MadScienceZone/readerboard/hardware/busylight/lighttree-smd.pdf

## lighttree-smd.pcb

## 1. Table of Contents (This Page) Created on Mon Sep 30 00:39:18 2024 2. top 3. bottom 4. outline 5. plated-drill 6. componentmask 7. soldermask 8. topsilk 9. bottomsilk 10. toppaste 11. bottompaste 12. topassembly 13. bottomassembly 14. fab

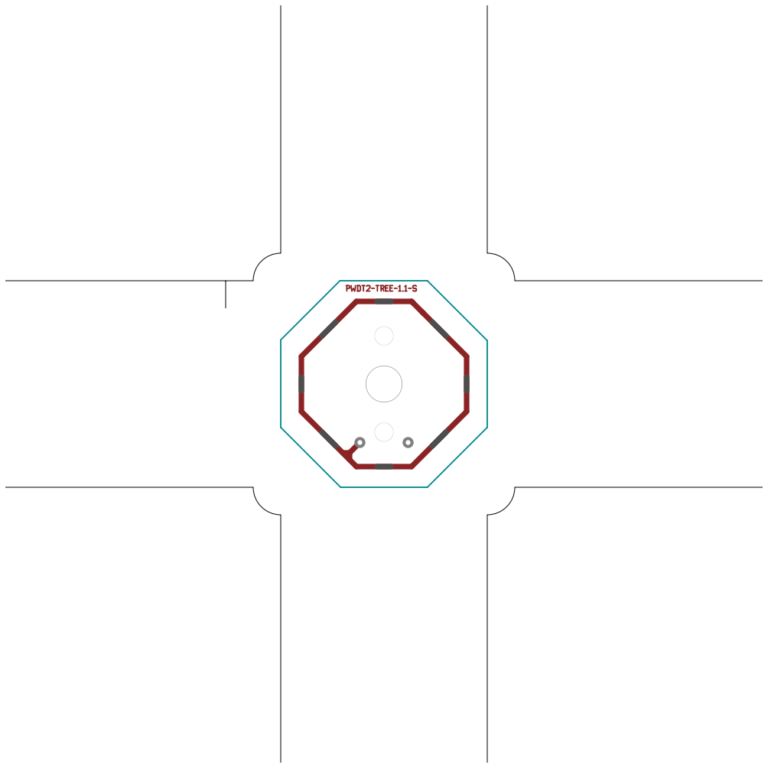
[picture p21: figure]

top, scale = 1:1.000

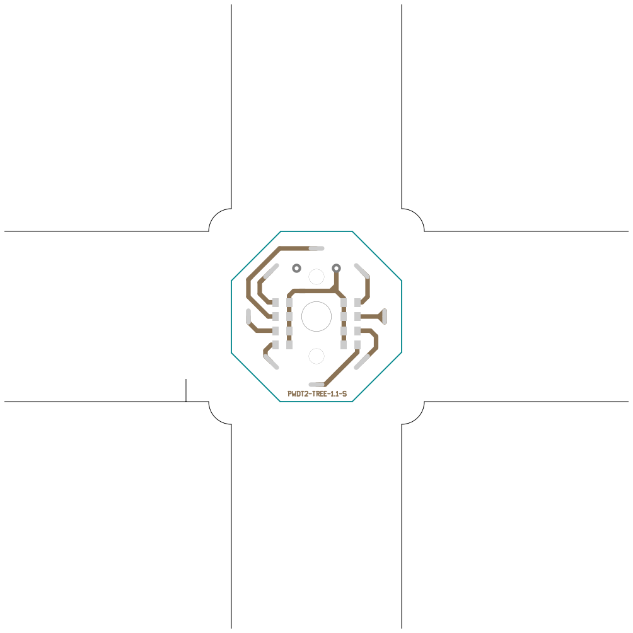
[picture p22: figure]

bottom (mirrored), scale = 1:1.000

outline, scale = 1:1.000 plated-drill, scale = 1:1.000

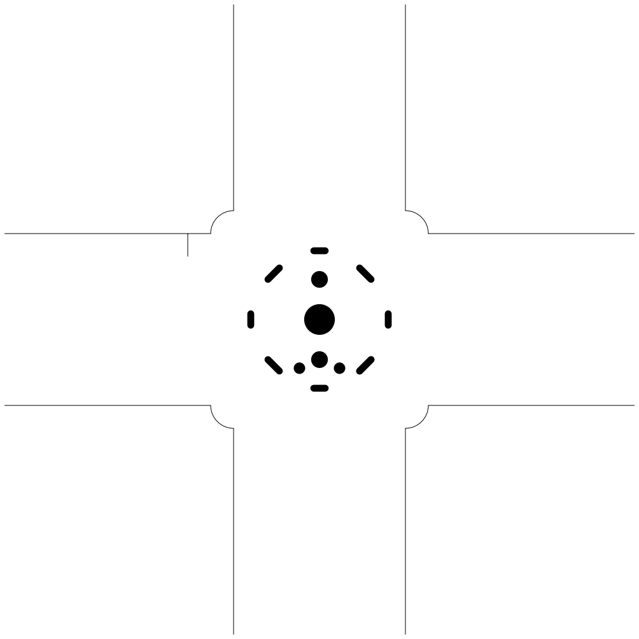
[picture p23: figure]

topmask, scale = 1:1.000

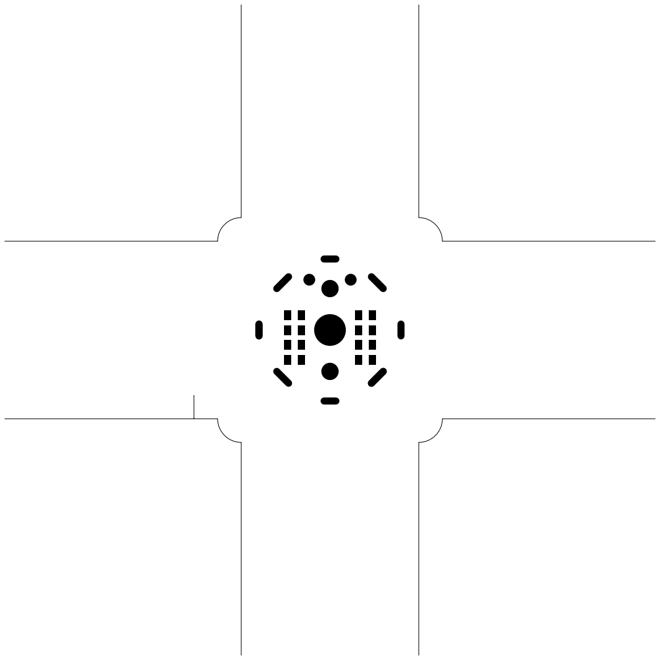
[picture p24: figure]

bottommask (mirrored), scale = 1:1.000

topsilk, scale = 1:1.000 bottomsilk (mirrored), scale = 1:1.000

toppaste, scale = 1:1.000 bottompaste (mirrored), scale = 1:1.000

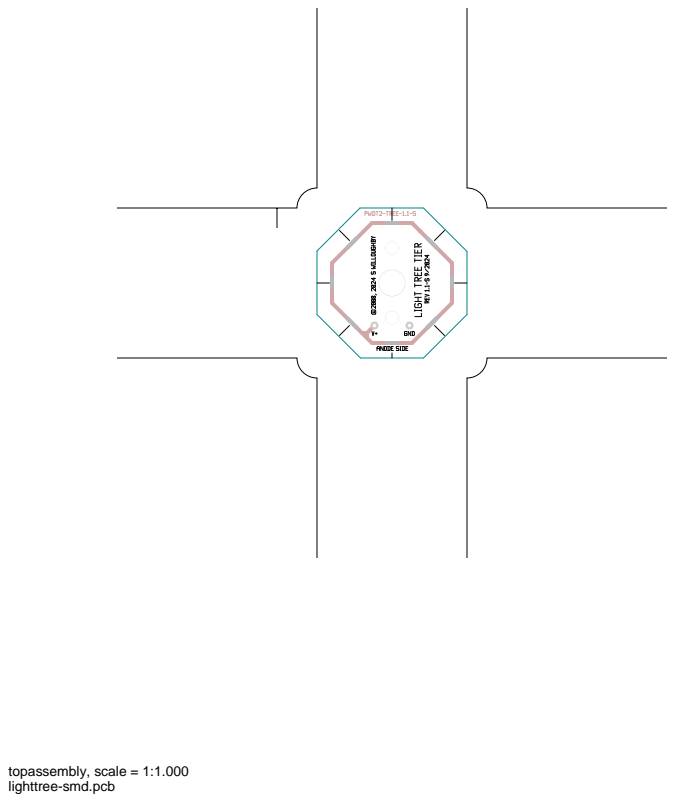
[picture p25: page 12]
topassembly, scale = 1:1.000

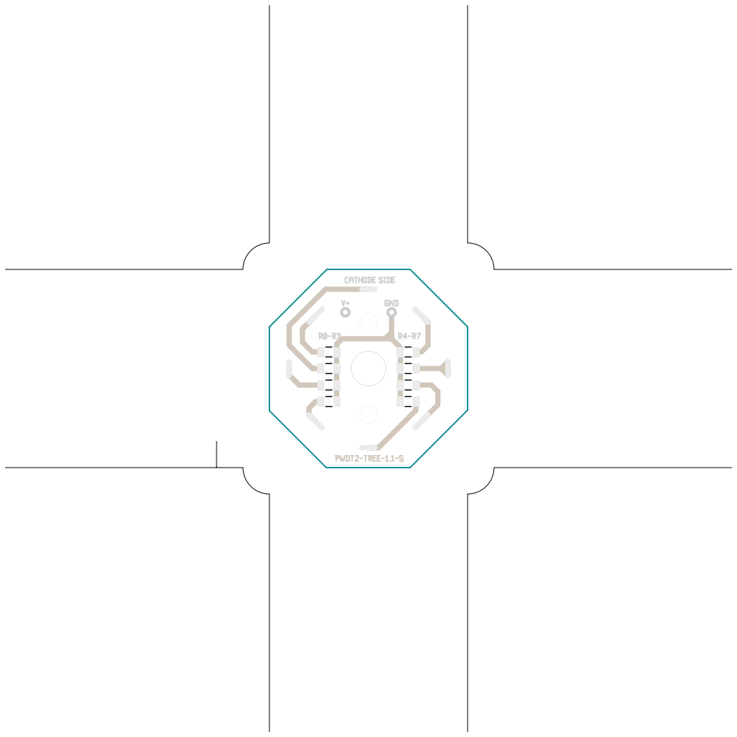
[picture p26: figure]

bottomassembly (mirrored), scale = 1:1.000

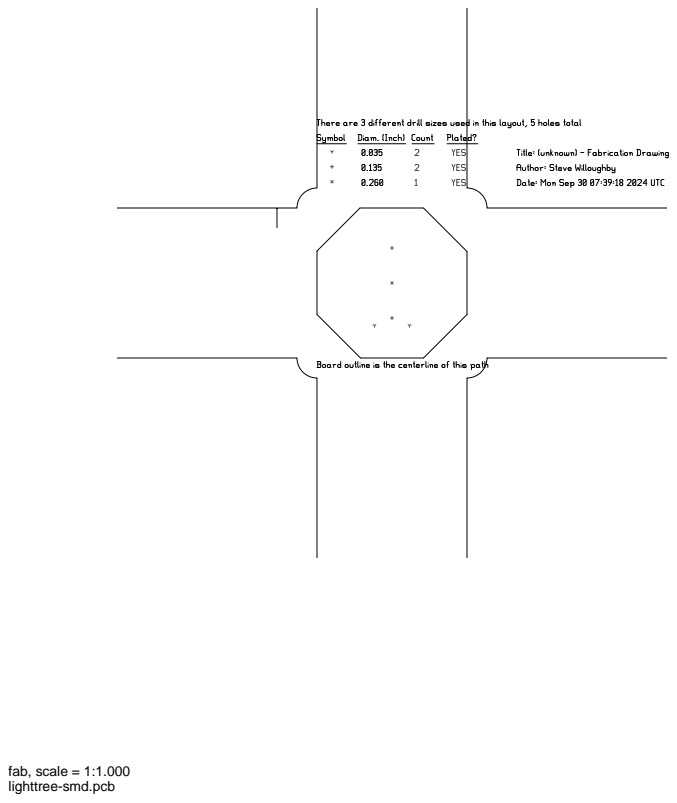
[picture p27: page 14]
fab, scale = 1:1.000
