MadScienceZone/readerboard/hardware/busylight/lighttree.pdf

## lighttree.pcb

## 1. Table of Contents (This Page) Created on Mon Sep 30 00:38:34 2024 2. top 3. bottom 4. outline 5. plated-drill 6. componentmask 7. soldermask 8. topsilk 9. bottomsilk 10. toppaste 11. bottompaste 12. topassembly 13. bottomassembly 14. fab

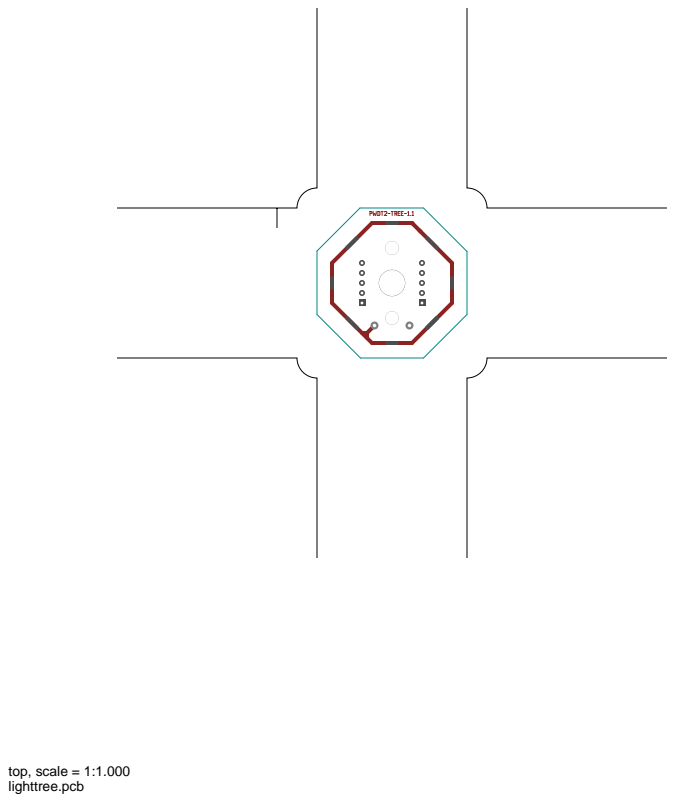
[picture p28: page 2]
top, scale = 1:1.000

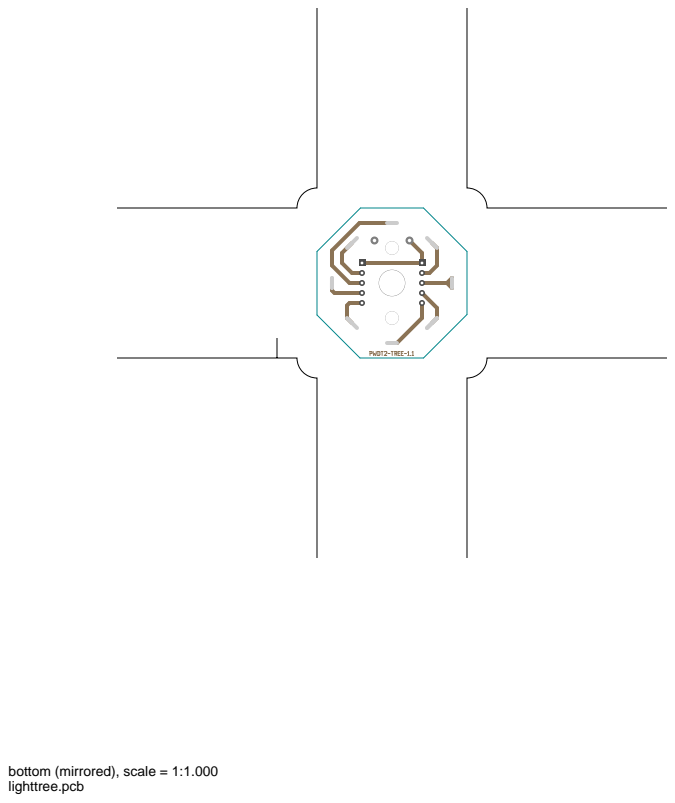
[picture p29: page 3]

bottom (mirrored), scale = 1:1.000

outline, scale = 1:1.000 plated-drill, scale = 1:1.000

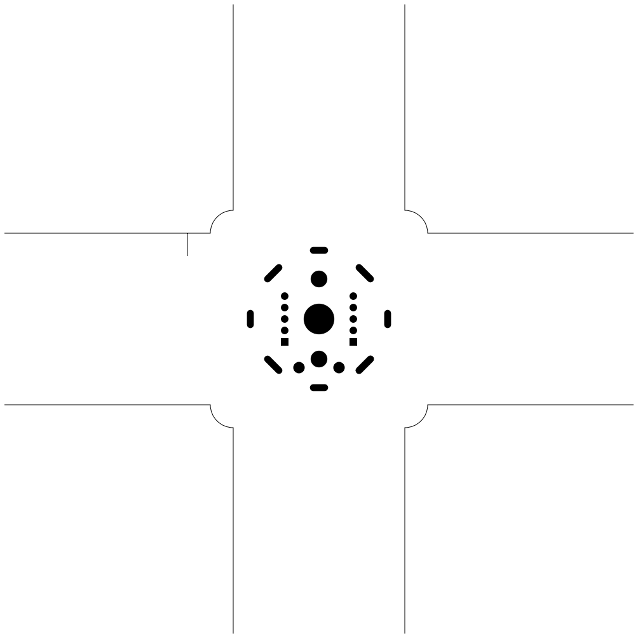
[picture p30: figure]

topmask, scale = 1:1.000

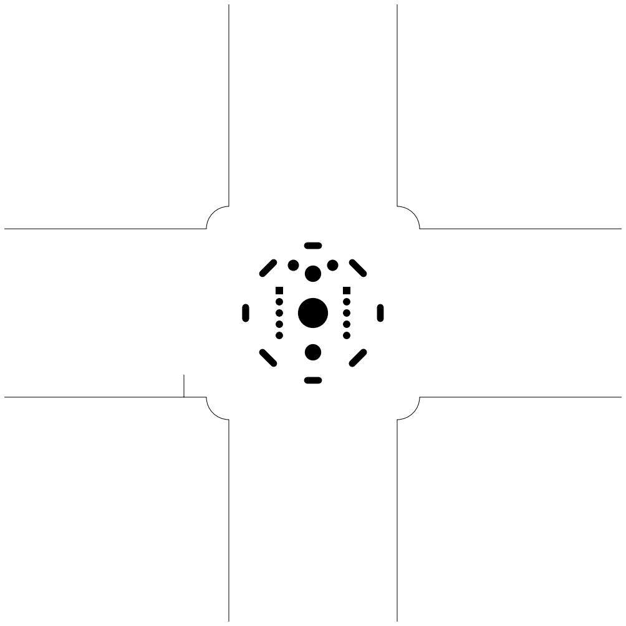
[picture p31: figure]

bottommask (mirrored), scale = 1:1.000

topsilk, scale = 1:1.000 bottomsilk (mirrored), scale = 1:1.000

toppaste, scale = 1:1.000 bottompaste (mirrored), scale = 1:1.000

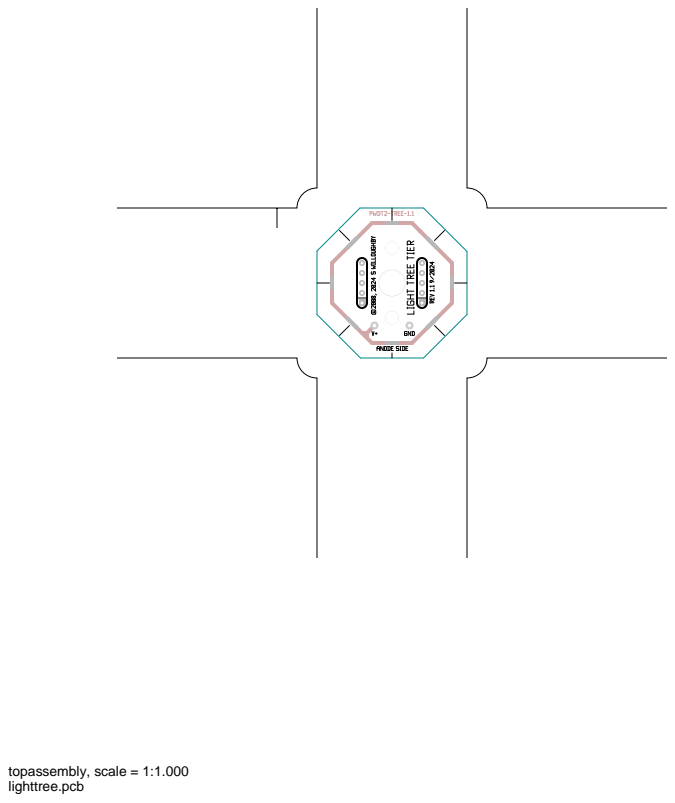
[picture p32: page 12]
topassembly, scale = 1:1.000

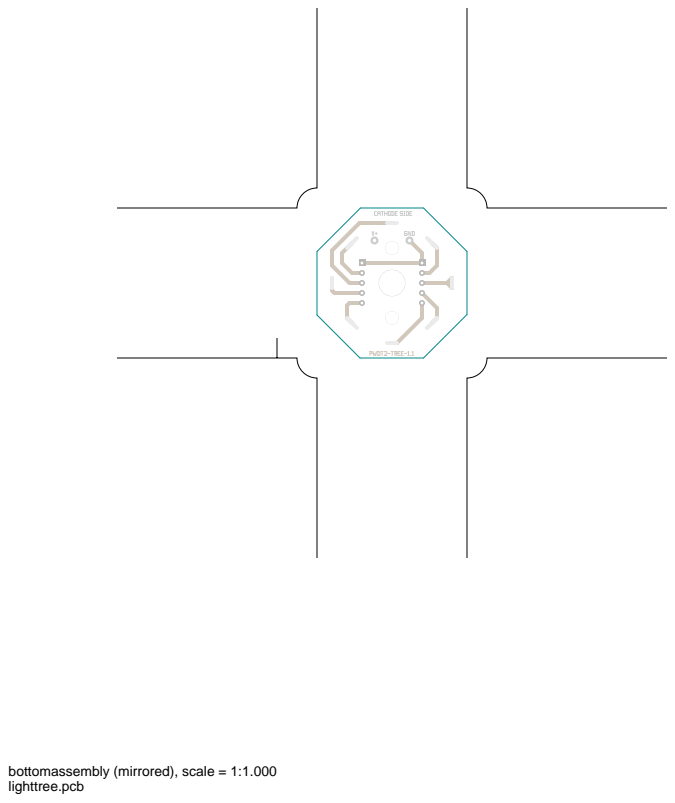
[picture p33: page 13]

bottomassembly (mirrored), scale = 1:1.000

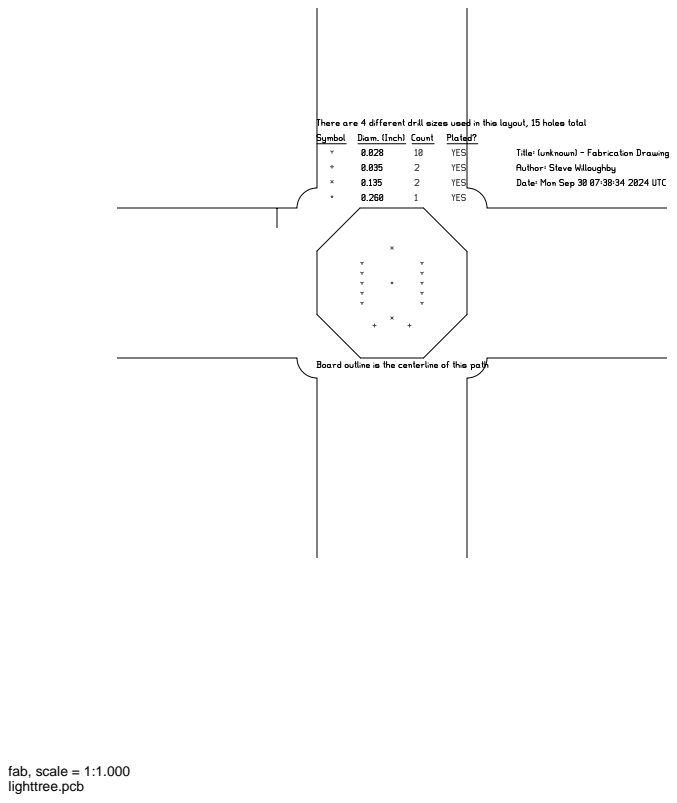
[picture p34: page 14]
fab, scale = 1:1.000
