MadScienceZone/readerboard/man/man1/setsn.pdf

SETSN(1) | General Commands Manual | SETSN(1)

NAME
setsn − Field program a newserial number into a device SYNOPSIS
setsn [−model type] −port name −sn serialno −speed rate
DESCRIPTION
After flashing a newfirmware image onto a newReaderboard or Busylight device, use this program to configure a unique serial number into its EEPROM.
OPTIONS
−model type
Specifies the hardware type being programmed. The value of type may be rb (the default), mono, or busylight, or any ofthe values which are accepted by rbserver(1)’sconfiguration file in the DeviceType field of the Devices list. While not strictly required, specifying this parameter may make it easier for setsn to correctly verify that the serial number has successfully been set.

−port name
Specifies the serial port’sdevice name on the system through which the device may be reached.

−sn serialno
The serial number to be set on the device. This must be no more than six characters, and should be plain ASCII characters, preferably alphanumerics. Serial numbers B00000−B00299 and RB0000−RB0299 are reserved for use by the original author.

−speed rate
Sets the baud rate at which to communicate with the target device.
AUTHOR
Steve Willoughby / steve@madscience.zone.
COPYRIGHT
Copyright © 2024 by Steven L. Willoughby,Aloha, Oregon, USA. All Rights Reserved. Distributed under the BSD 3-Clause License.
29-Sep-2024 | Readerboard/Busylight Project | 1
