MadScienceZone/readerboard/legacy/README.md

This directory contains the legacy Busylight support programs which have not yet been
converted to the combined busylight+readerboard model, where they will work hand-in-hand
with `rbserver` to update a set of devices.
