MadScienceZone/readerboard/doc/images/busylight_tree-assembly-0.png

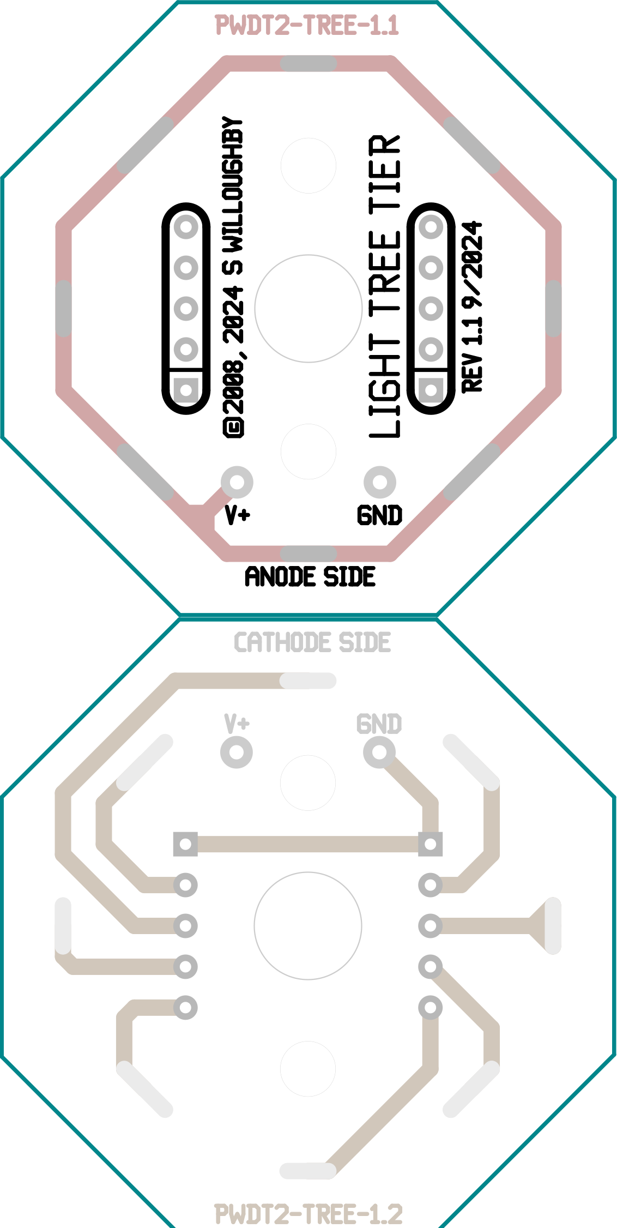
doc/images/busylight_tree-assembly-0.png
