MadScienceZone/readerboard/hardware/ada/adashield.kicad_sch

## KiCad design hardware/ada/adashield.kicad_sch (2024-10-30)

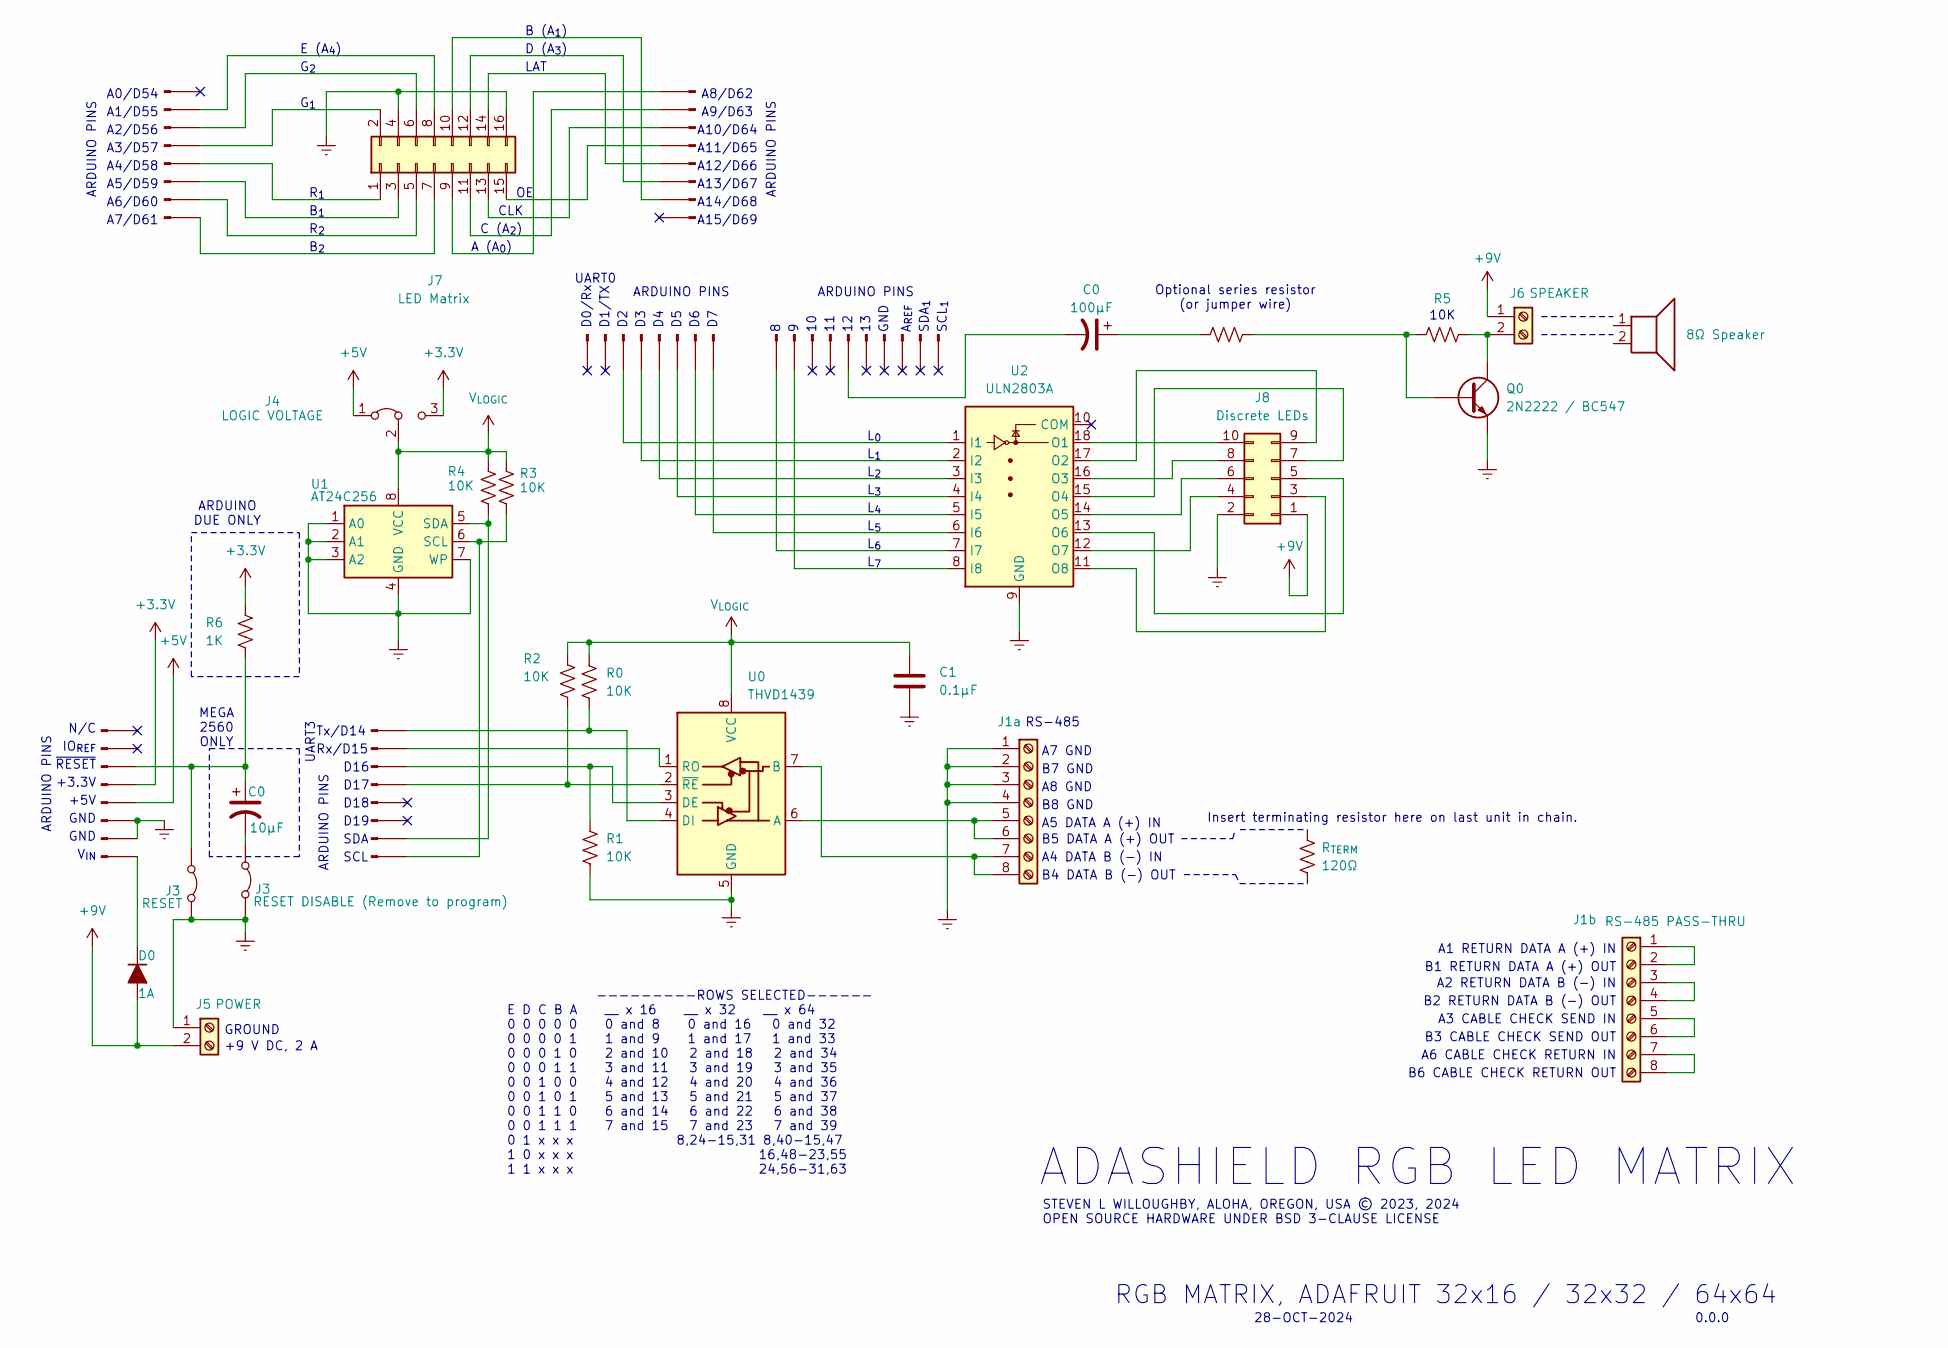
[picture p107: schematic adashield.kicad_sch]

Parts:
C0: 100μF
C1: 0.1µF
D0: 1A
J1a: Screw_Terminal_01x08
J1b: RS-485 PASS-THRU
J3, J4: Conn_01x08_Pin
J5: POWER
J6: SPEAKER
J7: LED Matrix
J8: Discrete LEDs
LS1: 8Ω Speaker
Q0: 2N2222 / BC547
R0, R1, R2, R3, R4: 10K
R5, R55: R_US
R6: 1K
R_{TERM}: 120Ω
U0: THVD1439; SOIC-8_3.9x4.9mm_P1.27mm
U1: AT24C256; SOIC-8_3.9x4.9mm_P1.27mm
U2: ULN2803A

Connections:
+3.3V: J3.4, J4.3 (B), R6.1
+5V: J3.5, J4.1 (A)
+9V: D0.2 (A), J5.2, J6.1, J8.1
Earth: J7.4, J7.16
GNDREF: C1.2, J1a.1, J1a.2, J1a.3, J1a.4, J3.2 (B), J3.6, J3.7, J5.1, J8.2, Q0.3 (E), R1.2, U0.5 (GND), U1.1 (A0), U1.2 (A1), U1.3 (A2), U1.4 (GND), U1.7 (WP), U2.9 (GND)
unnamed: C0.1, J3.1 (A), J3.3, R6.2, R55.1
unnamed: C0.2, J3.1 (A)
unnamed: D0.1 (K), J3.8
unnamed: J1a.5, J1a.6, U0.6 (A)
unnamed: J1a.7, J1a.8, U0.7 (B)
unnamed: J1b.1, J1b.2
unnamed: J1b.3, J1b.4
unnamed: J1b.5, J1b.6
unnamed: J1b.7, J1b.8
unnamed: J4.1 (A), R0.2, U0.4 (DI)
unnamed: J4.2 (C), U0.1 (RO)
unnamed: J4.3 (B), R1.1, U0.3 (DE)
unnamed: J4.4, R2.2, U0.2 (~RE)
unnamed: J4.7, R4.2, U1.5 (SDA)
unnamed: J4.8, R3.2, U1.6 (SCL)
unnamed: J6.2, Q0.1 (C), R5.2
unnamed: J8.3, U2.11 (O8)
unnamed: J8.4, U2.12 (O7)
unnamed: J8.5, U2.13 (O6)
unnamed: J8.6, U2.14 (O5)
unnamed: J8.7, U2.15 (O4)
unnamed: J8.8, U2.16 (O3)
unnamed: J8.9, U2.17 (O2)
unnamed: J8.10, U2.18 (O1)
unnamed: Q0.2 (B), R5.1, R55.2
V_{LOGIC}: C1.1, J4.2 (C), R0.1, R2.1, R3.1, R4.1, U0.8 (VCC), U1.8 (VCC)

Notes on the sheet:
C (A_{2})
B4 DATA B (-) OUT
A0/D54
28-OCT-2024
+5V
ARDUINO PINS
ARDUINO DUE ONLY
A10/D64
A13/D67
B_{1}
CLK
GND
RS-485
UART0
SDA
A3/D57
RGB MATRIX, ADAFRUIT 32x16 / 32x32 / 64x64
A9/D63
G_{1}
A14/D68
SCL
0.0.0
A6 CABLE CHECK RETURN IN
R_{2}
A7/D61
---------ROWS SELECTED------ E D C B A __ x 16 __ x 32 __ x 64 0 0 0 0 0 0 and 8 0 and 16 0 and 32 0 0 0 0 1 1 and 9 1 and 17 1 and 33 0 0 0 1 0 2 and 10 2 and 18 2 and 34 0 0 0 1 1 3 and 11 3 and 19 3 and 35 0 0 1 0 0 4 and 12 4 and 20 4 and 36 0 0 1 0 1 5 and 13 5 and 21 5 and 37 0 0 1 1 0 6 and 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
B1 RETURN DATA A (+) OUT
L_{2}
A7 GND
B (A_{1})
D18
Optional series resistor (or jumper wire)
A3 CABLE CHECK SEND IN
A8/D62
A_{REF}
L_{5}
B8 GND
+9 V DC, 2 A
STEVEN L WILLOUGHBY, ALOHA, OREGON, USA © 2023, 2024 OPEN SOURCE HARDWARE UNDER BSD 3-CLAUSE LICENSE
MEGA 2560 ONLY
A11/D65
D1/TX
B5 DATA A (+) OUT
B_{2}
GROUND
Tx/D14
D0/Rx
A4 DATA B (-) IN
R_{1}
LAT
L_{6}
L_{3}
A1 RETURN DATA A (+) IN
L_{4}
SCL_{1}
B7 GND
10K
~{RESET}
E (A_{4})
B2 RETURN DATA B (-) OUT
N/C
D16
A5 DATA A (+) IN
Rx/D15
A (A_{0})
D19
A8 GND
A2 RETURN DATA B (-) IN
L_{0}
B6 CABLE CHECK RETURN OUT
A5/D59
+3.3V
A12/D66
IO_{REF}
L_{7}
B3 CABLE CHECK SEND OUT
D (A_{3})
L_{1}
A1/D55
ADASHIELD RGB LED MATRIX
A4/D58
G_{2}
A2/D56
D17
V_{IN}
SDA_{1}
UART3
Insert terminating resistor here on last unit in chain.
A15/D69
A6/D60
