MadScienceZone/readerboard/hardware/ada/adashield_qs.kicad_sch

## KiCad design hardware/ada/adashield_qs.kicad_sch (2024-10-29)

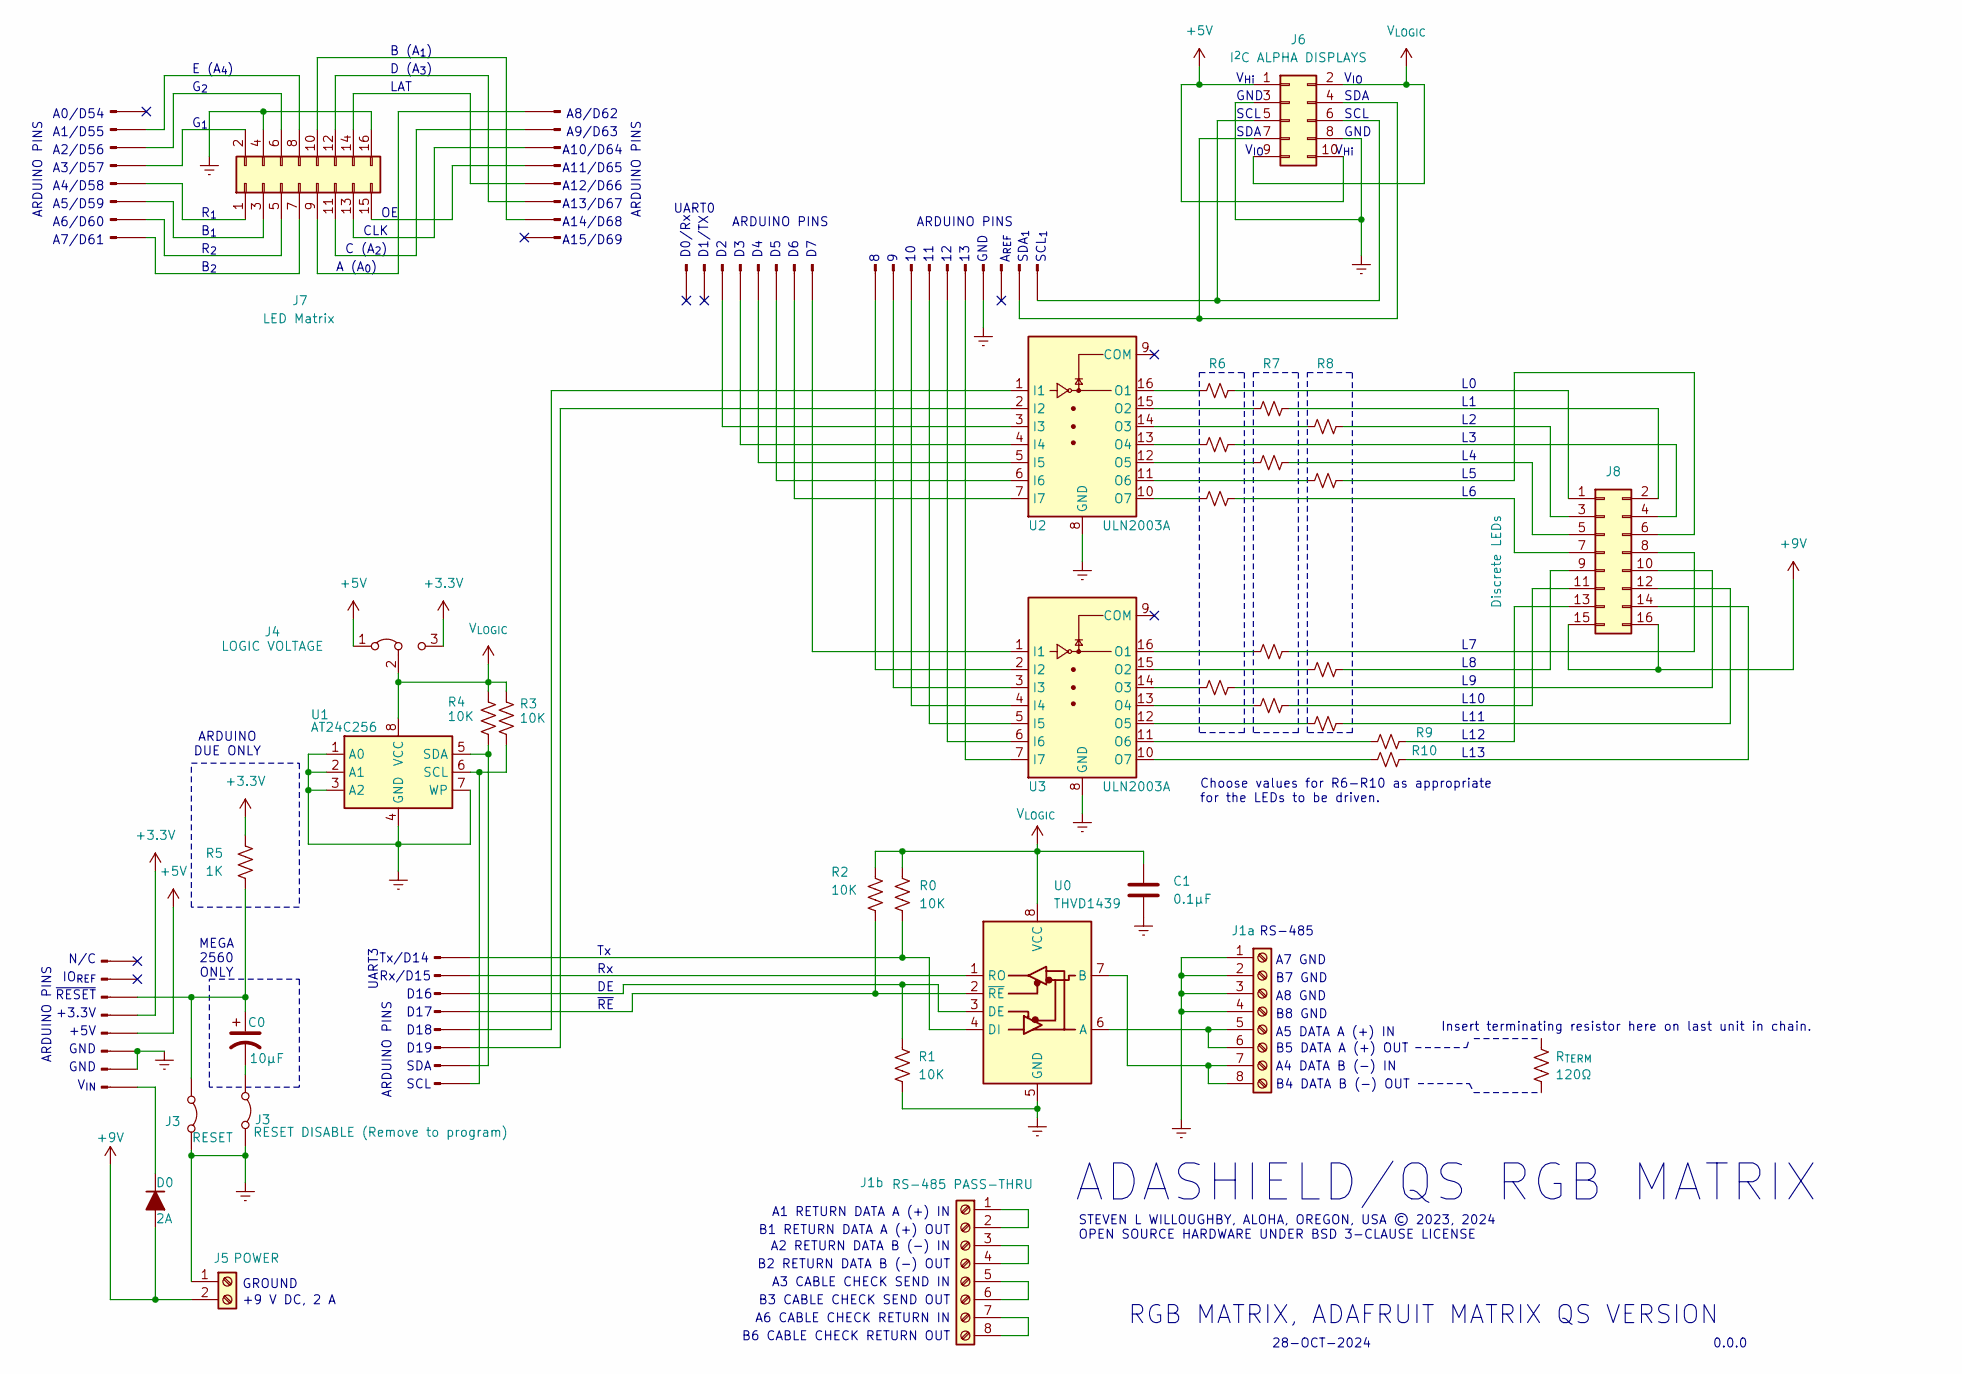
[picture p108: schematic adashield_qs.kicad_sch]

Parts:
C0: 10µF
C1: 0.1µF
D0: 2A
J1a: Screw_Terminal_01x08
J1b: RS-485 PASS-THRU
J3, J4: Conn_01x08_Pin
J5: POWER
J6: I^{2}C ALPHA DISPLAYS
J7: LED Matrix
J8: Discrete LEDs
R0, R1, R2, R3, R4: 10K
R5: 1K
R6, R7, R8, R9, R10, R11, R12, R13, R15, R16, R17: R_Small_US
R_{TERM}: 120Ω
U0: THVD1439; SOIC-8_3.9x4.9mm_P1.27mm
U1: AT24C256; SOIC-8_3.9x4.9mm_P1.27mm
U2, U3: ULN2003A

Connections:
+3.3V: J3.4, J4.3 (B), R5.1
+5V: J3.5, J4.1 (A), J6.1, J6.10
+9V: D0.2 (A), J5.2, J8.15, J8.16
Earth: J7.4, J7.16
GNDREF: C1.2, J1a.1, J1a.2, J1a.3, J1a.4, J3.2 (B), J3.6, J3.7, J5.1, J6.3, J6.8, R1.2, U0.5 (GND), U1.1 (A0), U1.2 (A1), U1.3 (A2), U1.4 (GND), U1.7 (WP), U2.8 (GND), U3.8 (GND)
unnamed: C0.1, J3.1 (A), J3.3, R5.2
unnamed: C0.2, J3.1 (A)
unnamed: D0.1 (K), J3.8
unnamed: J1a.5, J1a.6, U0.6 (A)
unnamed: J1a.7, J1a.8, U0.7 (B)
unnamed: J1b.1, J1b.2
unnamed: J1b.3, J1b.4
unnamed: J1b.5, J1b.6
unnamed: J1b.7, J1b.8
unnamed: J4.1 (A), R0.2, U0.4 (DI)
unnamed: J4.2 (C), U0.1 (RO)
unnamed: J4.3 (B), R1.1, U0.3 (DE)
unnamed: J4.4, R2.2, U0.2 (~RE)
unnamed: J4.5, U2.1 (I1)
unnamed: J4.6, U2.2 (I2)
unnamed: J4.7, R4.2, U1.5 (SDA)
unnamed: J4.8, R3.2, U1.6 (SCL)
unnamed: J6.4, J6.7
unnamed: J6.5, J6.6
unnamed: J8.1, R6.2
unnamed: J8.2, R7.2
unnamed: J8.3, R8.2
unnamed: J8.4, R7.2
unnamed: J8.5, R11.2
unnamed: J8.6, R15.2
unnamed: J8.7, R8.2
unnamed: J8.8, R12.2
unnamed: J8.9, R16.2
unnamed: J8.10, R9.2
unnamed: J8.11, R13.2
unnamed: J8.12, R17.2
unnamed: J8.13, R9.2
unnamed: J8.14, R10.2
unnamed: R6.1, U2.16 (O1)
unnamed: R7.1, U2.13 (O4), U2.15 (O2)
unnamed: R8.1, U2.10 (O7), U2.14 (O3)
unnamed: R9.1, U3.11 (O6), U3.14 (O3)
unnamed: R10.1, U3.10 (O7)
unnamed: R11.1, U2.12 (O5)
unnamed: R12.1, U3.16 (O1)
unnamed: R13.1, U3.13 (O4)
unnamed: R15.1, U2.11 (O6)
unnamed: R16.1, U3.15 (O2)
unnamed: R17.1, U3.12 (O5)
V_{LOGIC}: C1.1, J4.2 (C), J6.2, J6.9, R0.1, R2.1, R3.1, R4.1, U0.8 (VCC), U1.8 (VCC)

Notes on the sheet:
C (A_{2})
B4 DATA B (-) OUT
A0/D54
28-OCT-2024
L12
+5V
ARDUINO PINS
ARDUINO DUE ONLY
A10/D64
A13/D67
B_{1}
CLK
GND
L13
RS-485
UART0
SDA
L10
A3/D57
RGB MATRIX, ADAFRUIT MATRIX QS VERSION
A9/D63
G_{1}
~{RE}
A14/D68
SCL
0.0.0
A6 CABLE CHECK RETURN IN
V_{IO}
R_{2}
A7/D61
B1 RETURN DATA A (+) OUT
Choose values for R6-R10 as appropriate for the LEDs to be driven.
A7 GND
B (A_{1})
D18
A3 CABLE CHECK SEND IN
A8/D62
A_{REF}
B8 GND
+9 V DC, 2 A
STEVEN L WILLOUGHBY, ALOHA, OREGON, USA © 2023, 2024 OPEN SOURCE HARDWARE UNDER BSD 3-CLAUSE LICENSE
MEGA 2560 ONLY
A11/D65
D1/TX
B5 DATA A (+) OUT
B_{2}
GROUND
Tx/D14
D0/Rx
A4 DATA B (-) IN
R_{1}
V_{Hi}
LAT
A1 RETURN DATA A (+) IN
SCL_{1}
B7 GND
L11
~{RESET}
E (A_{4})
B2 RETURN DATA B (-) OUT
N/C
D16
A5 DATA A (+) IN
Rx/D15
A (A_{0})
D19
A8 GND
A2 RETURN DATA B (-) IN
B6 CABLE CHECK RETURN OUT
A5/D59
+3.3V
A12/D66
IO_{REF}
B3 CABLE CHECK SEND OUT
D (A_{3})
A1/D55
ADASHIELD/QS RGB MATRIX
A4/D58
G_{2}
A2/D56
D17
V_{IN}
SDA_{1}
UART3
Insert terminating resistor here on last unit in chain.
A15/D69
A6/D60
