MadScienceZone/readerboard/hardware/busylight/busylight.kicad_sch

## KiCad design hardware/busylight/busylight.kicad_sch (2024-10-28)

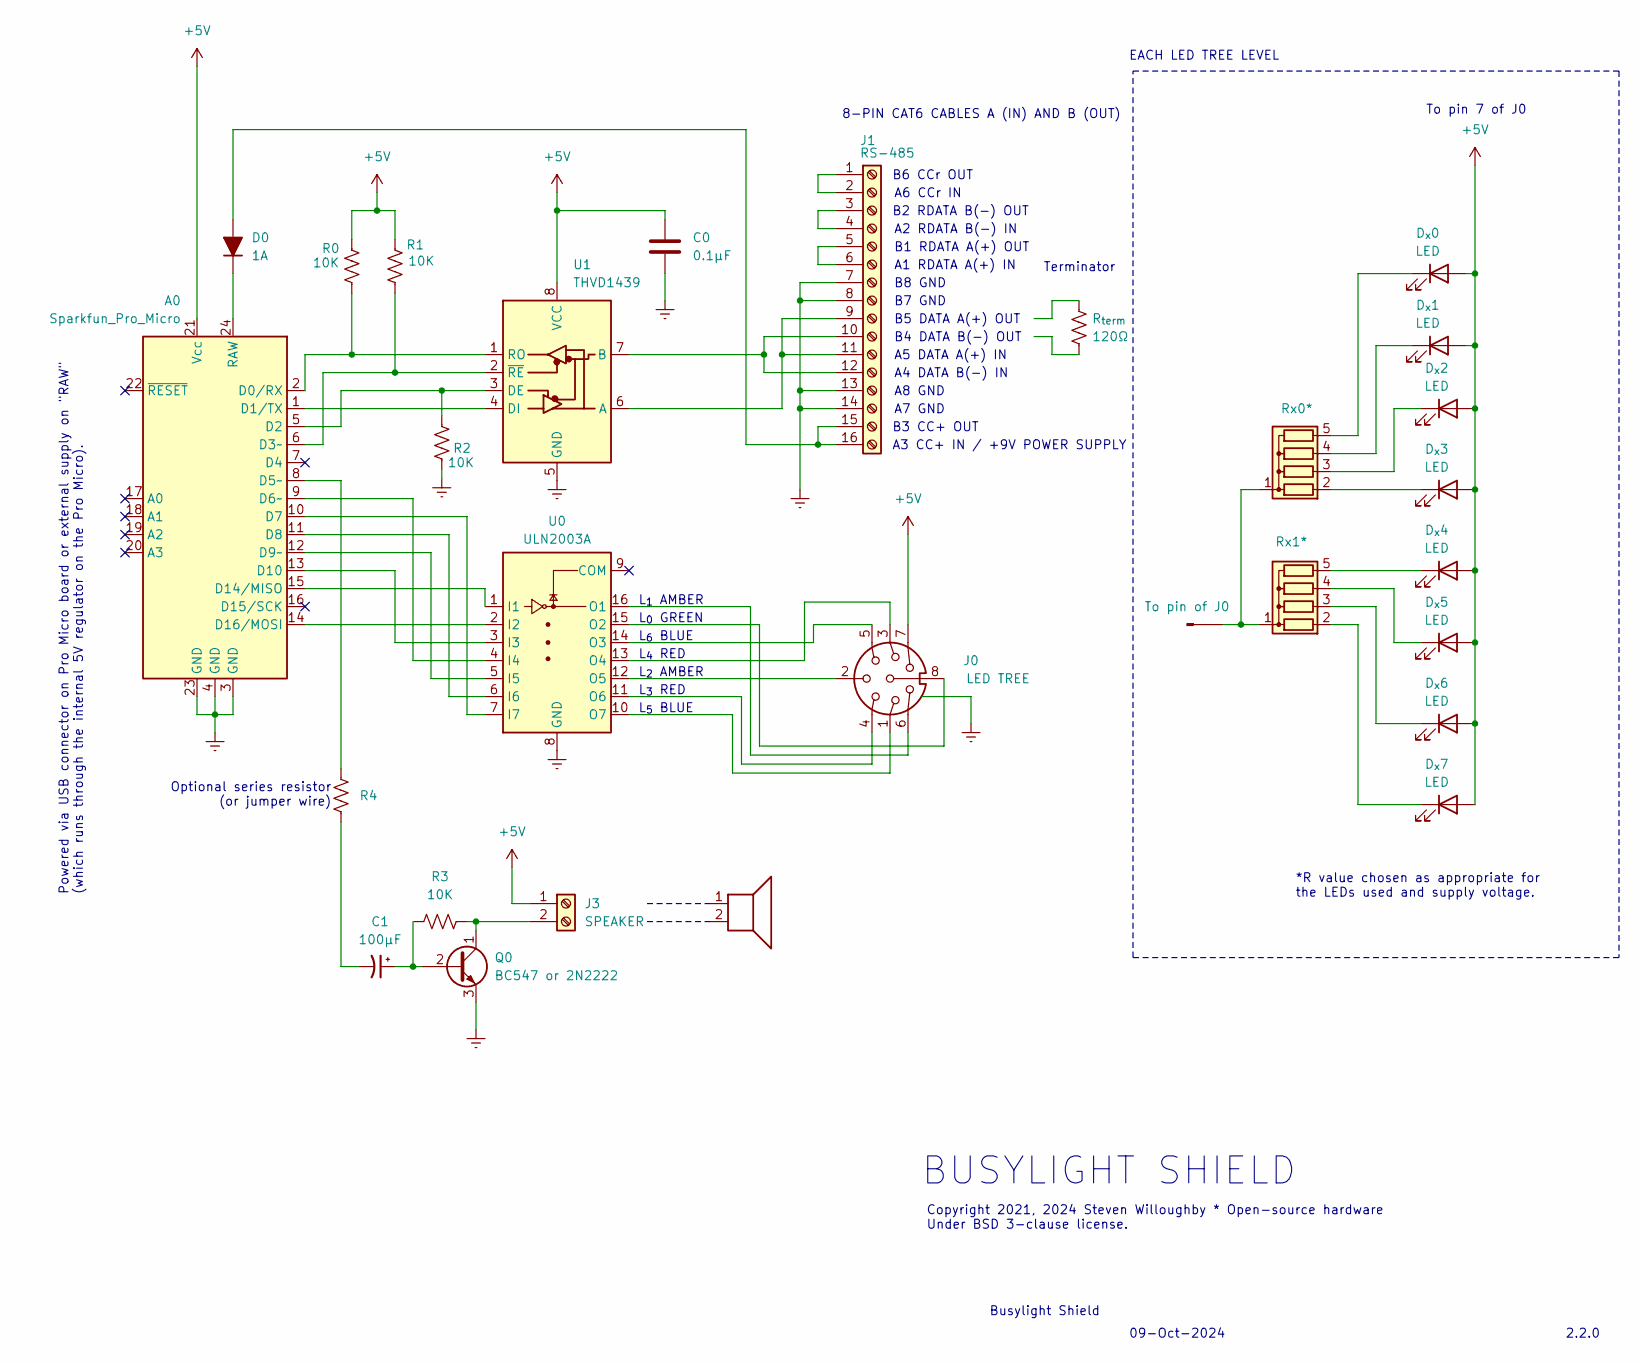
[picture p109: schematic busylight.kicad_sch]

Parts:
A0: Sparkfun_Pro_Micro
C0: 0.1μF
C1: 100μF
D0: 1A
D_{x}0, D_{x}1, D_{x}2, D_{x}3, D_{x}4, D_{x}5, D_{x}6, D_{x}7: LED
J0: LED TREE
J1: RS-485
J2: To pin of J0
J3: SPEAKER
LS1: Speaker
Q0: BC547 or 2N2222; TO-92_Inline
R0, R1, R2, R3, R4: 10K
R_{term}: 120Ω
Rx0*, Rx1*: R_Network04; R_Array_SIP5
U0: ULN2003A
U1: THVD1439; SOIC-8_3.9x4.9mm_P1.27mm

Connections:
+5V: A0.21 (Vcc), C0.1, D_{x}0.2 (A), D_{x}1.2 (A), D_{x}2.2 (A), D_{x}3.2 (A), D_{x}4.2 (A), D_{x}5.2 (A), D_{x}6.2 (A), D_{x}7.2 (A), J0.7, J3.1, R0.1, R1.1, U1.8 (VCC)
Earth: A0.3 (GND), A0.4 (GND), A0.23 (GND), C0.2, J1.7, J1.8, J1.13, J1.14, Q0.3 (E), R2.2, U0.8 (GND), U1.5 (GND)
unnamed: A0.1 (D1/TX), U1.4 (DI)
unnamed: A0.2 (D0/RX), R0.2, U1.1 (RO)
unnamed: A0.5 (D2), R2.1, U1.3 (DE)
unnamed: A0.6 (D3~), R1.2, U1.2 (~RE)
unnamed: A0.8 (D5~), R4.2
unnamed: A0.9 (D6~), U0.4 (I4)
unnamed: A0.10 (D7), U0.7 (I7)
unnamed: A0.11 (D8), U0.6 (I6)
unnamed: A0.12 (D9~), U0.5 (I5)
unnamed: A0.13 (D10), U0.3 (I3)
unnamed: A0.14 (D16/MOSI), U0.2 (I2)
unnamed: A0.15 (D14/MISO), U0.1 (I1)
unnamed: A0.24 (RAW), D0.1 (K)
unnamed: C1.1, Q0.2 (B), R3.2
unnamed: C1.2, R4.1
unnamed: D0.2 (A), J1.15, J1.16
unnamed: D_{x}0.1 (K), Rx0*.5 (R4)
unnamed: D_{x}1.1 (K), Rx0*.4 (R3)
unnamed: D_{x}2.1 (K), Rx0*.3 (R2)
unnamed: D_{x}3.1 (K), Rx0*.2 (R1)
unnamed: D_{x}4.1 (K), Rx1*.5 (R4)
unnamed: D_{x}5.1 (K), Rx1*.4 (R3)
unnamed: D_{x}6.1 (K), Rx1*.3 (R2)
unnamed: D_{x}7.1 (K), Rx1*.2 (R1)
unnamed: J0.1, U0.10 (O7)
unnamed: J0.2, U0.12 (O5)
unnamed: J0.3, U0.13 (O4)
unnamed: J0.4, U0.11 (O6)
unnamed: J0.5, U0.14 (O3)
unnamed: J0.6, U0.16 (O1)
unnamed: J0.8, U0.15 (O2)
unnamed: J1.1, J1.2
unnamed: J1.3, J1.4
unnamed: J1.5, J1.6
unnamed: J1.10, J1.12, U1.7 (B)
unnamed: J1.9, J1.11, U1.6 (A)
unnamed: J2.1, Rx0*.1 (common), Rx1*.1 (common)
unnamed: J3.2, Q0.1 (C), R3.1

Notes on the sheet:
B7 GND
L_{6} BLUE
L_{1} AMBER
09-Oct-2024
B3 CC+ OUT
8-PIN CAT6 CABLES A (IN) AND B (OUT)
A4 DATA B(-) IN
A5 DATA A(+) IN
A2 RDATA B(-) IN
Copyright 2021, 2024 Steven Willoughby * Open-source hardware Under BSD 3-clause license.
L_{3} RED
A1 RDATA A(+) IN
Busylight Shield
L_{5} BLUE
Terminator
A8 GND
L_{2} AMBER
To pin 7 of J0
B2 RDATA B(-) OUT
A3 CC+ IN / +9V POWER SUPPLY
B1 RDATA A(+) OUT
A6 CCr IN
Powered via USB connector on Pro Micro board or external supply on "RAW" (which runs through the internal 5V regulator on the Pro Micro).
EACH LED TREE LEVEL
B8 GND
L_{0} GREEN
B5 DATA A(+) OUT
Optional series resistor (or jumper wire)
2.2.0
B4 DATA B(-) OUT
BUSYLIGHT SHIELD
B6 CCr OUT
*R value chosen as appropriate for the LEDs used and supply voltage.
A7 GND
L_{4} RED
