MadScienceZone/readerboard/hardware/readerboard/readerboard.kicad_sch

## KiCad design hardware/readerboard/readerboard.kicad_sch (2024-10-28)

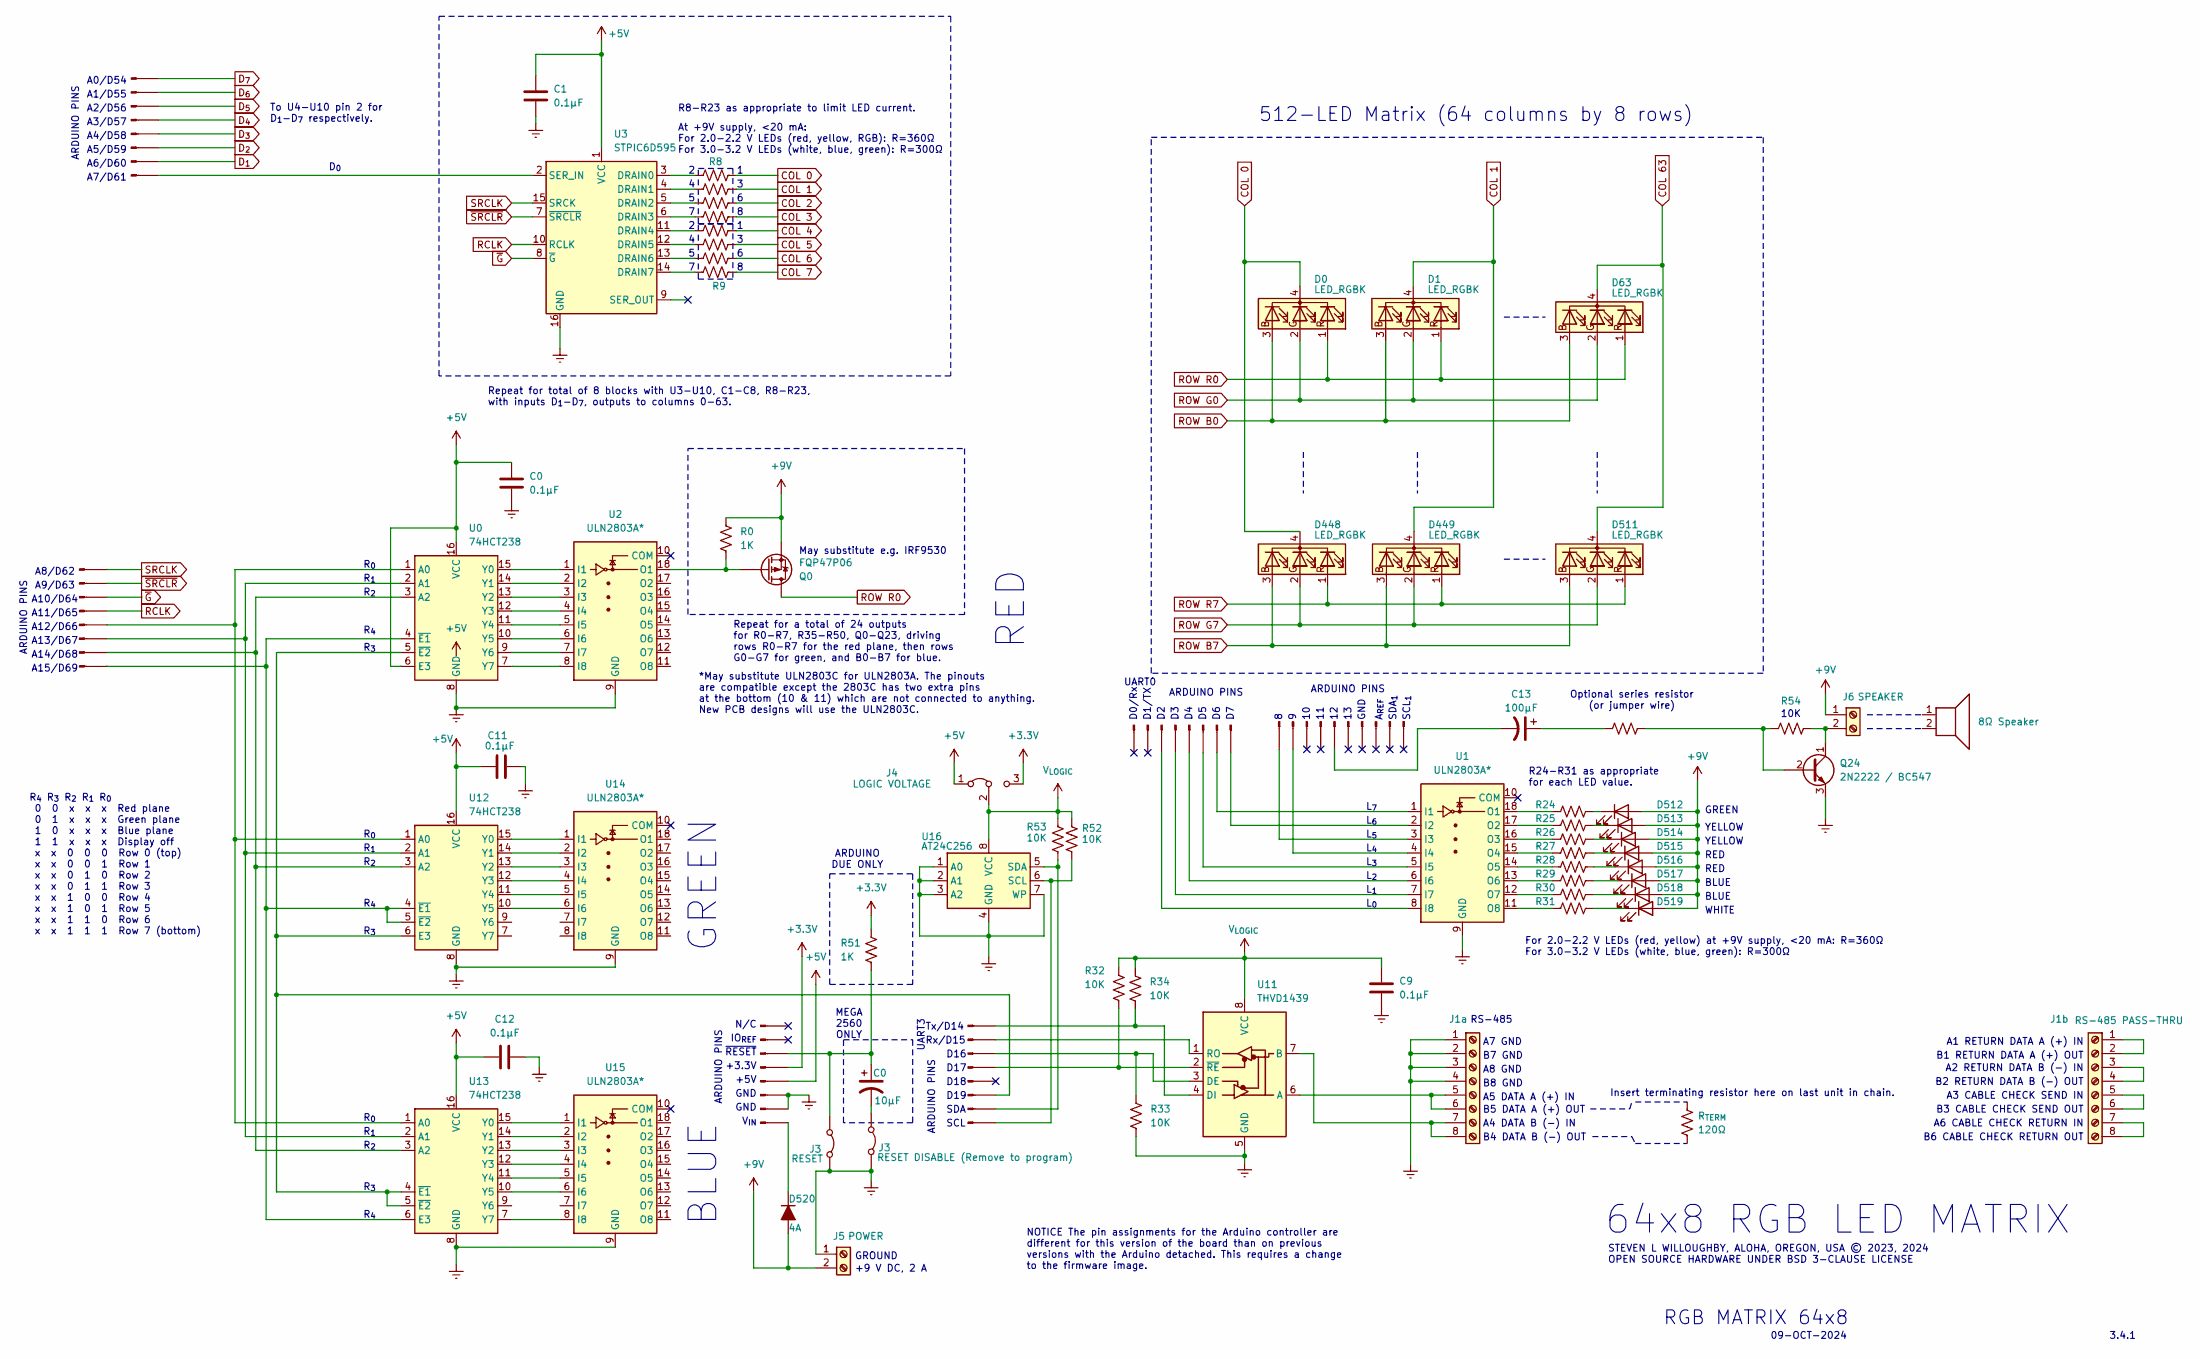
[picture p110: schematic readerboard.kicad_sch]

Parts:
C0, C1, C9, C11, C12: 0.1µF
C13: 100μF
D0, D1, D63, D448, D449, D511: LED_RGBK
D512, D513, D514, D515, D516, D517, D518, D519: LED
D520: 4A
J1a: Screw_Terminal_01x08
J1b: RS-485 PASS-THRU
J3, J4: Conn_01x08_Pin
J5: POWER
J6: SPEAKER
LS1: 8Ω Speaker
Q0: FQP47P06; TO-220-3_Vertical
Q24: 2N2222 / BC547
R0, R51: 1K
R8, R9, R10, R11, R12, R13, R14, R24, R25, R26, R27, R28, R29, R30, R31, R54, R55: R_US
R32, R33, R34, R52, R53: 10K
R_{TERM}: 120Ω
U0, U12, U13: 74HCT238
U1, U2, U14, U15: ULN2803A*
U3: STPIC6D595
U11: THVD1439; SOIC-8_3.9x4.9mm_P1.27mm
U16: AT24C256; SOIC-8_3.9x4.9mm_P1.27mm

Connections:
+3.3V: J3.4, J4.3 (B), R51.1
+5V: C0.1, C1.1, C11.1, C12.1, J3.5, J4.1 (A), U0.6 (E3), U0.16 (VCC), U3.1 (VCC), U12.16 (VCC), U13.16 (VCC)
+9V: D512.2 (A), D513.2 (A), D514.2 (A), D515.2 (A), D516.2 (A), D517.2 (A), D518.2 (A), D519.2 (A), D520.2 (A), J5.2, J6.1, Q0.3 (S), R0.1
COL 0: D0.4 (K), D448.4 (K), R8.2
COL 1: D1.4 (K), D449.4 (K), R9.2
COL 2: R10.2
COL 3: R11.2
COL 4: R12.2
COL 5: R13.2
COL 6: R14.2
COL 7: R9.2
COL 63: D63.4 (K), D511.4 (K)
GNDREF: C0.2, C1.2, C9.2, C11.2, C12.2, J1a.1, J1a.2, J1a.3, J1a.4, J3.2 (B), J3.6, J3.7, J5.1, Q24.3 (E), R33.2, U0.8 (GND), U1.9 (GND), U2.9 (GND), U3.16 (GND), U11.5 (GND), U12.8 (GND), U13.8 (GND), U14.9 (GND), U15.9 (GND), U16.1 (A0), U16.2 (A1), U16.3 (A2), U16.4 (GND), U16.7 (WP)
unnamed: C0.1, J3.1 (A), J3.3, R51.2
unnamed: C0.2, J3.1 (A)
unnamed: C13.1, R55.1
unnamed: D512.1 (K), R24.2
unnamed: D513.1 (K), R25.2
unnamed: D514.1 (K), R26.2
unnamed: D515.1 (K), R27.2
unnamed: D516.1 (K), R28.2
unnamed: D517.1 (K), R29.2
unnamed: D518.1 (K), R30.2
unnamed: D519.1 (K), R31.2
unnamed: D520.1 (K), J3.8
unnamed: J1a.5, J1a.6, U11.6 (A)
unnamed: J1a.7, J1a.8, U11.7 (B)
unnamed: J1b.1, J1b.2
unnamed: J1b.3, J1b.4
unnamed: J1b.5, J1b.6
unnamed: J1b.7, J1b.8
unnamed: J4.1 (A), R34.2, U11.4 (DI)
unnamed: J4.2 (C), U11.1 (RO)
unnamed: J4.3 (B), R33.1, U11.3 (DE)
unnamed: J4.4, R32.2, U11.2 (~RE)
unnamed: J4.6, U0.5 (~E2), U12.6 (E3), U13.4 (~E1), U13.5 (~E2)
unnamed: J4.7, R53.2, U16.5 (SDA)
unnamed: J4.8, R52.2, U16.6 (SCL)
unnamed: J6.2, Q24.1 (C), R54.2
unnamed: Q0.1 (G), R0.2, U2.18 (O1)
unnamed: Q24.2 (B), R54.1, R55.2
unnamed: R8.1, U3.3 (DRAIN0)
unnamed: R9.1, U3.4 (DRAIN1), U3.14 (DRAIN7)
unnamed: R10.1, U3.5 (DRAIN2)
unnamed: R11.1, U3.6 (DRAIN3)
unnamed: R12.1, U3.11 (DRAIN4)
unnamed: R13.1, U3.12 (DRAIN5)
unnamed: R14.1, U3.13 (DRAIN6)
unnamed: R24.1, U1.18 (O1)
unnamed: R25.1, U1.17 (O2)
unnamed: R26.1, U1.16 (O3)
unnamed: R27.1, U1.15 (O4)
unnamed: R28.1, U1.14 (O5)
unnamed: R29.1, U1.13 (O6)
unnamed: R30.1, U1.12 (O7)
unnamed: R31.1, U1.11 (O8)
unnamed: U0.1 (A0), U12.1 (A0), U13.1 (A0)
unnamed: U0.2 (A1), U12.2 (A1), U13.2 (A1)
unnamed: U0.3 (A2), U12.3 (A2), U13.3 (A2)
unnamed: U0.4 (~E1), U12.4 (~E1), U12.5 (~E2), U13.6 (E3)
unnamed: U0.7 (Y7), U2.8 (I8)
unnamed: U0.9 (Y6), U2.7 (I7)
unnamed: U0.10 (Y5), U2.6 (I6)
unnamed: U0.11 (Y4), U2.5 (I5)
unnamed: U0.12 (Y3), U2.4 (I4)
unnamed: U0.13 (Y2), U2.3 (I3)
unnamed: U0.14 (Y1), U2.2 (I2)
unnamed: U0.15 (Y0), U2.1 (I1)
unnamed: U12.10 (Y5), U14.6 (I6)
unnamed: U12.11 (Y4), U14.5 (I5)
unnamed: U12.12 (Y3), U14.4 (I4)
unnamed: U12.13 (Y2), U14.3 (I3)
unnamed: U12.14 (Y1), U14.2 (I2)
unnamed: U12.15 (Y0), U14.1 (I1)
unnamed: U13.7 (Y7), U15.8 (I8)
unnamed: U13.10 (Y5), U15.6 (I6)
unnamed: U13.11 (Y4), U15.5 (I5)
unnamed: U13.12 (Y3), U15.4 (I4)
unnamed: U13.13 (Y2), U15.3 (I3)
unnamed: U13.14 (Y1), U15.2 (I2)
unnamed: U13.15 (Y0), U15.1 (I1)
RCLK: U3.10 (RCLK)
ROW B0: D0.3 (BA), D1.3 (BA), D63.3 (BA)
ROW B7: D448.3 (BA), D449.3 (BA), D511.3 (BA)
ROW G0: D0.2 (GA), D1.2 (GA), D63.2 (GA)
ROW G7: D448.2 (GA), D449.2 (GA), D511.2 (GA)
ROW R0: D0.1 (RA), D1.1 (RA), D63.1 (RA), Q0.2 (D)
ROW R7: D448.1 (RA), D449.1 (RA), D511.1 (RA)
SRCLK: U3.15 (SRCK)
V_{LOGIC}: C9.1, J4.2 (C), R32.1, R34.1, R52.1, R53.1, U11.8 (VCC), U16.8 (VCC)
~G: U3.8 (~G)
~SRCLR: U3.7 (~SRCLR)

Notes on the sheet:
R_{3}
B4 DATA B (-) OUT
R_{1}
A0/D54
GREEN
For 2.0-2.2 V LEDs (red, yellow) at +9V supply, <20 mA: R=360Ω For 3.0-3.2 V LEDs (white, blue, green): R=300Ω
R_{2}
BLUE
NOTICE The pin assignments for the Arduino controller are different for this version of the board than on previous versions with the Arduino detached. This requires a change to the firmware image.
09-OCT-2024
+5V
ARDUINO PINS
ARDUINO DUE ONLY
A10/D64
RED
A13/D67
To U4-U10 pin 2 for D_{1}-D_{7} respectively.
GND
RS-485
UART0
R_{4} R_{3} R_{2} R_{1} R_{0} 0 0 x x x Red plane 0 1 x x x Green plane 1 0 x x x Blue plane 1 1 x x x Display off x x 0 0 0 Row 0 (top) x x 0 0 1 Row 1 x x 0 1 0 Row 2 x x 0 1 1 Row 3 x x 1 0 0 Row 4 x x 1 0 1 Row 5 x x 1 1 0 Row 6 x x 1 1 1 Row 7 (bottom)
SDA
Repeat for total of 8 blocks with U3-U10, C1-C8, R8-R23, with inputs D_{1}-D_{7}, outputs to columns 0-63.
A3/D57
YELLOW
RGB MATRIX 64x8
*May substitute ULN2803C for ULN2803A. The pinouts are compatible except the 2803C has two extra pins at the bottom (10 & 11) which are not connected to anything. New PCB designs will use the ULN2803C.
A9/D63
A14/D68
SCL
3.4.1
A6 CABLE CHECK RETURN IN
512-LED Matrix (64 columns by 8 rows)
R_{4}
A7/D61
B1 RETURN DATA A (+) OUT
L_{2}
R_{0}
A7 GND
D18
Optional series resistor (or jumper wire)
A3 CABLE CHECK SEND IN
A8/D62
A_{REF}
L_{5}
B8 GND
Repeat for a total of 24 outputs for R0-R7, R35-R50, Q0-Q23, driving rows R0-R7 for the red plane, then rows G0-G7 for green, and B0-B7 for blue.
+9 V DC, 2 A
STEVEN L WILLOUGHBY, ALOHA, OREGON, USA © 2023, 2024 OPEN SOURCE HARDWARE UNDER BSD 3-CLAUSE LICENSE
MEGA 2560 ONLY
A11/D65
D1/TX
WHITE
B5 DATA A (+) OUT
GROUND
Tx/D14
D0/Rx
R24-R31 as appropriate for each LED value.
A4 DATA B (-) IN
L_{6}
L_{3}
May substitute e.g. IRF9530
A1 RETURN DATA A (+) IN
L_{4}
SCL_{1}
B7 GND
10K
~{RESET}
R8-R23 as appropriate to limit LED current.
B2 RETURN DATA B (-) OUT
N/C
D_{0}
D16
A5 DATA A (+) IN
Rx/D15
D19
A8 GND
A2 RETURN DATA B (-) IN
L_{0}
B6 CABLE CHECK RETURN OUT
A5/D59
+3.3V
A12/D66
At +9V supply, <20 mA: For 2.0-2.2 V LEDs (red, yellow, RGB): R=360Ω For 3.0-3.2 V LEDs (white, blue, green): R=300Ω
IO_{REF}
L_{7}
B3 CABLE CHECK SEND OUT
L_{1}
A1/D55
64x8 RGB LED MATRIX
A4/D58
A2/D56
D17
V_{IN}
SDA_{1}
UART3
Insert terminating resistor here on last unit in chain.
A15/D69
A6/D60
