MadScienceZone/readerboard/firmware/readerboard/fonts.ino

#include "fonts.h"
#if !IS_READERBOARD
const int N_FONTS = 0;
const word FontMaxCodepoint[1] = {0};
const unsigned char * const GlyphMetricDataLengths[1] = {NULL};
const unsigned char * const GlyphMetricDataSpaces[1] = {NULL};
const unsigned short * const GlyphMetricDataOffsets[1] = {NULL};
const unsigned short * const GlyphMetricDataHeights[1] = {NULL};
const PROGMEM byte CharacterBitmap[1] = {0};
bool get_font_metric_data(byte font, byte codepoint, unsigned char *height, unsigned char *leng, unsigned char *space, unsigned short *offset)
{
      return false;
}
byte get_font_bitmap_data(unsigned long offset) 
{
      return 0;
}
#else
/* Generated font data -- do not edit this file directly; your changes will be lost!
 *   Font #0 generated from standard.font
 *   Font #1 generated from standard_variable.font
 *   Font #2 generated from symbol.font
 *   Font #3 generated from double.font
 *   Font #4 generated from led16.font
 *   Font #5 generated from led16a.font
 */

/* font definitions */

const int N_FONTS = 6;

const word FontMaxCodepoint[N_FONTS] = {255, 255, 183, 190, 57, 57};


const PROGMEM unsigned char GlyphMetricDataFont0Lengths[256] = {
 5,  5,  5,  5,  5,  5,  5,  5,  5,  5,  5,  5,  5,  5,  5,  5,  5,  5,  5,  5, 
 5,  5,  5,  5,  5,  5,  5,  5,  5,  5,  5,  5,  0,  3,  4,  5,  5,  5,  5,  3, 
 5,  3,  5,  5,  2,  5,  2,  5,  5,  5,  5,  5,  5,  5,  5,  5,  5,  5,  2,  2, 
 4,  5,  5,  5,  5,  5,  5,  5,  5,  5,  5,  5,  5,  5,  5,  5,  5,  5,  5,  5, 
 5,  5,  5,  5,  5,  5,  5,  5,  5,  5,  5,  5,  5,  3,  5,  5,  5,  5,  5,  5, 
 5,  5,  5,  5,  5,  4,  5,  4,  4,  5,  5,  5,  5,  5,  5,  5,  5,  5,  5,  5, 
 5,  5,  5,  5,  3,  5,  5,  6,  5,  5,  5,  2,  5,  5,  5,  3,  5,  4,  5,  5, 
 5,  5,  5,  5,  5,  5,  5,  5,  5,  5,  5,  5,  5,  5,  5,  5,  6,  5,  5,  5, 
 0,  3,  5,  5,  5,  5,  3,  5,  5,  5,  5,  5,  5,  4,  5,  5,  4,  5,  3,  3, 
 5,  5,  5,  4,  5,  3,  4,  5,  5,  5,  5,  5,  5,  5,  5,  5,  5,  5,  5,  5, 
 5,  5,  5,  5,  5,  5,  5,  5,  5,  5,  5,  5,  5,  5,  5,  5,  5,  5,  5,  5, 
 5,  5,  5,  5,  5,  5,  5,  5,  5,  5,  5,  5,  5,  5,  5,  5,  4,  4,  4,  4, 
 5,  5,  5,  5,  5,  5,  5,  5,  5,  5,  5,  5,  5,  5,  5,  5, };
const PROGMEM unsigned char GlyphMetricDataFont1Lengths[256] = {
 5,  5,  5,  5,  5,  5,  5,  5,  5,  5,  5,  5,  5,  5,  5,  5,  5,  5,  5,  5, 
 5,  5,  5,  5,  5,  5,  5,  5,  5,  5,  5,  5,  0,  1,  4,  5,  5,  5,  5,  3, 
 3,  3,  5,  5,  2,  5,  2,  5,  5,  5,  5,  5,  5,  5,  5,  5,  5,  5,  2,  2, 
 4,  5,  5,  5,  5,  5,  5,  5,  5,  5,  5,  5,  5,  3,  5,  5,  5,  7,  6,  5, 
 5,  5,  5,  5,  5,  5,  5,  7,  5,  5,  5,  3,  5,  3,  5,  5,  3,  5,  5,  5, 
 5,  5,  5,  5,  5,  3,  5,  4,  3,  5,  5,  5,  5,  5,  5,  5,  5,  5,  5,  5, 
 5,  5,  5,  5,  1,  5,  5,  6,  5,  5,  2,  2,  5,  5,  5,  3,  5,  3,  5,  5, 
 5,  5,  5,  7,  5,  5,  5,  5,  5,  5,  5,  5,  5,  5,  5,  5,  8,  8,  5,  5, 
 0,  1,  5,  5,  5,  5,  1,  5,  5,  5,  5,  5,  5,  4,  5,  5,  4,  5,  3,  3, 
 5,  5,  5,  3,  2,  3,  4,  5,  5,  5,  5,  5,  5,  5,  5,  5,  5,  5,  9,  5, 
 5,  5,  5,  5,  3,  3,  3,  3,  5,  5,  5,  5,  5,  5,  5,  5,  5,  5,  5,  5, 
 5,  5,  5,  5,  5,  5,  5,  5,  5,  5,  9,  5,  5,  5,  5,  5,  3,  3,  3,  3, 
 5,  5,  5,  5,  5,  5,  5,  5,  5,  5,  5,  5,  5,  5,  5,  5, };
const PROGMEM unsigned char GlyphMetricDataFont2Lengths[184] = {
 5,  5,  5,  5,  5,  5,  5,  5,  5,  5,  5,  5,  5,  5,  5,  5,  5,  5,  5,  5, 
 5,  5,  5,  5,  5,  5,  5,  5,  5,  5,  5,  5,  0,  3,  5,  5,  5,  5,  5,  5, 
 5,  5,  5,  5,  2,  2,  2,  2,  6,  6,  6,  6,  6,  6,  6,  6,  6,  6,  2,  5, 
 5,  5,  5,  5,  7,  6,  7,  7,  7,  6,  6,  7,  6,  2,  4,  7,  5,  8,  7,  6, 
 6,  7,  6,  6,  6,  6,  7,  8,  6,  6,  6,  5,  5,  5,  5,  5,  8,  8,  8,  8, 
 8,  8,  8,  8,  8,  8,  8,  5,  5,  8,  8,  5,  8,  7,  7,  5,  5,  5,  4,  4, 
 8,  4,  4,  5,  5,  5,  7,  7,  5,  5,  5,  5,  6,  5,  5,  6,  5,  5,  7,  7, 
 5,  8,  7,  7, 10, 10,  8,  8,  9,  9,  5,  5,  8,  8,  8,  8,  8,  8,  8,  8, 
 0,  0,  0,  0,  0,  0,  0,  0,  0,  5,  5,  5,  5,  5,  5,  5,  8,  8,  8,  8, 
 8,  8,  8,  8, };
const PROGMEM unsigned char GlyphMetricDataFont3Lengths[191] = {
 5,  5,  5,  5,  5,  5,  5,  5,  5,  5,  5,  5,  5,  5,  5,  5,  5,  5,  5,  5, 
 5,  5,  5,  5,  5,  5,  5,  5,  5,  5,  5,  5,  0,  6, 10, 10, 10, 10, 11,  1, 
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
    0,  2468,     0,  2480,  2492,  2500,     0,     0,     0,     0, 
    0,     0,     0,     0,     0,     0,     0,     0,     0,     0, 
    0,     0,     0,     0,     0,     0,     0,     0,     0,     0, 
    0,     0,     0,     0,     0,     0,     0,     0,  2520,  2529, 
 2538,  2542,     0,     0,     0,     0,     0,     0,     0,     0, 
    0,     0,     0,     0,     0,     0,     0,     0,     0,     0, 
    0,     0,     0,     0,     0,     0,     0,     0,     0,     0, 
    0,     0,     0,     0,     0,     0,     0,     0,     0,     0, 
    0,     0,     0,     0,     0,     0,     0,     0,     0,     0, 
    0,     0,     0,     0,     0,     0,     0,     0,  2546,  2566, 
 2586, };
const PROGMEM unsigned short GlyphMetricDataFont4Offsets[58] = {
    0,     0,     0,     0,     0,     0,     0,     0,     0,     0, 
    0,     0,     0,     0,     0,     0,     0,     0,     0,     0, 
    0,     0,     0,     0,     0,     0,     0,     0,     0,     0, 
    0,     0,     0,     0,     0,     0,     0,     0,     0,     0, 
    0,     0,     0,     0,     0,     0,     0,     0,  2606,  2626, 
 2646,  2666,  2686,  2706,  2726,  2746,  2766,  2786, };
const PROGMEM unsigned short GlyphMetricDataFont5Offsets[58] = {
    0,     0,     0,     0,     0,     0,     0,     0,     0,     0, 
    0,     0,     0,     0,     0,     0,     0,     0,     0,     0, 
    0,     0,     0,     0,     0,     0,     0,     0,     0,     0, 
    0,     0,     0,     0,     0,     0,     0,     0,     0,     0, 
    0,     0,     0,     0,     0,     0,     0,     0,  2806,  2826, 
 2846,  2866,  2886,  2906,  2926,  2946,  2966,  2986, };
const unsigned char * const GlyphMetricDataHeights[6] = {GlyphMetricDataFont0Heights, GlyphMetricDataFont1Heights, GlyphMetricDataFont2Heights, GlyphMetricDataFont3Heights, GlyphMetricDataFont4Heights, GlyphMetricDataFont5Heights};
const unsigned char * const GlyphMetricDataLengths[6] = {GlyphMetricDataFont0Lengths, GlyphMetricDataFont1Lengths, GlyphMetricDataFont2Lengths, GlyphMetricDataFont3Lengths, GlyphMetricDataFont4Lengths, GlyphMetricDataFont5Lengths};
const unsigned char * const GlyphMetricDataSpaces[6] = {GlyphMetricDataFont0Spaces, GlyphMetricDataFont1Spaces, GlyphMetricDataFont2Spaces, GlyphMetricDataFont3Spaces, GlyphMetricDataFont4Spaces, GlyphMetricDataFont5Spaces};
const unsigned short * const GlyphMetricDataOffsets[6] = {GlyphMetricDataFont0Offsets, GlyphMetricDataFont1Offsets, GlyphMetricDataFont2Offsets, GlyphMetricDataFont3Offsets, GlyphMetricDataFont4Offsets, GlyphMetricDataFont5Offsets};
/* font bitmap data */
const PROGMEM byte CharacterBitmap[3006] = {
 0x3E, 0x22, 0x22, 0x22, 0x3E,
                                         // 0 - 4
                                         //     .....
                                         //     @@@@@
                                         //     @...@
                                         //     @...@
                                         //     @...@
                                         //     @@@@@
                                         //     .....
                                         //     .....
 0x00, 0x00, 0x5F,
                                         // 5 - 7
                                         //     ..@
                                         //     ..@
                                         //     ..@
                                         //     ..@
                                         //     ..@
                                         //     ...
                                         //     ..@
                                         //     ...
 0x00, 0x07, 0x00, 0x07,
                                         // 8 - 11
                                         //     .@.@
                                         //     .@.@
                                         //     .@.@
                                         //     ....
                                         //     ....
                                         //     ....
                                         //     ....
                                         //     ....
 0x14, 0x7F, 0x14, 0x7F, 0x14,
                                         // 12 - 16
                                         //     .@.@.
                                         //     .@.@.
                                         //     @@@@@
                                         //     .@.@.
                                         //     @@@@@
                                         //     .@.@.
                                         //     .@.@.
                                         //     .....
 0x46, 0x49, 0x7F, 0x49, 0x31,
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
                                         //     .@@@.
                                         //     ....@
                                         //     .@@@@
                                         //     @...@
                                         //     .@@@@
                                         //     .....
 0x20, 0x54, 0x56, 0x55, 0x78,
                                         // 892 - 896
                                         //     ...@.
                                         //     ..@..
                                         //     .@@@.
                                         //     ....@
                                         //     .@@@@
                                         //     @...@
                                         //     .@@@@
                                         //     .....
 0x20, 0x56, 0x55, 0x56, 0x78,
                                         // 897 - 901
                                         //     ..@..
                                         //     .@.@.
                                         //     .@@@.
                                         //     ....@
                                         //     .@@@@
                                         //     @...@
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
